ThomasStolt/Junior-Stair-Light-Project/images/IMG_2182.jpg

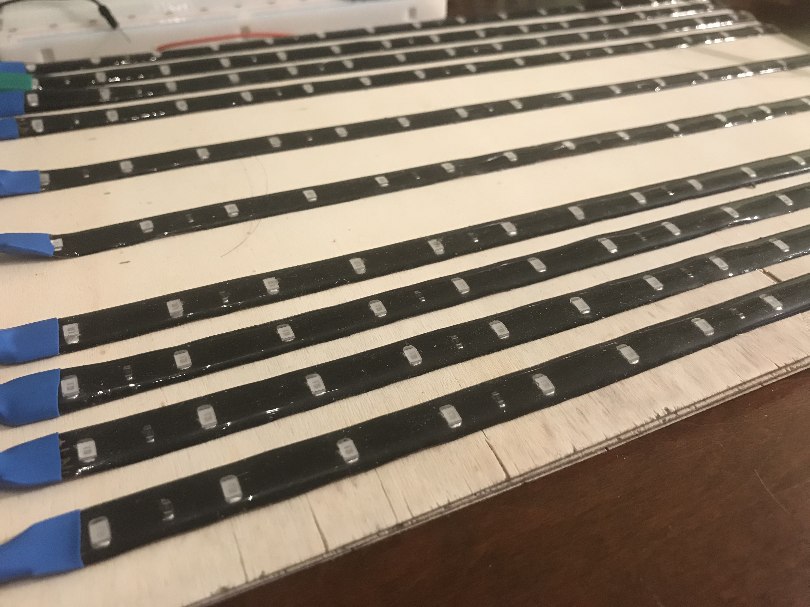
images/IMG_2182.jpg
